dementiev-net/uv-led-exposure/firmware/config.h

#ifndef CONFIG_H
#define CONFIG_H

#define BTN_DEBOUNCE      20   // дребезг кнопок (мсек.)
#define BTN_DCGAP         100  // время между двойным кликом (мсек.)
#define BTN_HOLDTIME      1000 // время зажатия кнопки (мсек.)
#define BTN_LONGHOLDTIME  3000 // время долгого нажатия кнопки  (мсек.)

#define SEC_STEP          5    // шаг энкодера (сек.)

#define BUZ_TONE          2000 // пищалка
#define BUZ_TIME1         200
#define BUZ_TIME2         500

#endif
